hipersys-team/lightning/rtl/sram/nonlinear_lut/log_lut.v

       log_lut[1] = 3; // log(32) = 3.4657359027997265
       log_lut[2] = 4; // log(64) = 4.1588830833596715
       log_lut[3] = 4; // log(96) = 4.564348191467836
       log_lut[4] = 4; // log(128) = 4.852030263919617
       log_lut[5] = 5; // log(160) = 5.075173815233827
       log_lut[6] = 5; // log(192) = 5.2574953720277815
       log_lut[7] = 5; // log(224) = 5.4116460518550396
       log_lut[8] = 5; // log(256) = 5.545177444479562
       log_lut[9] = 5; // log(288) = 5.662960480135946
       log_lut[10] = 5; // log(320) = 5.768320995793772
       log_lut[11] = 5; // log(352) = 5.863631175598097
       log_lut[12] = 5; // log(384) = 5.950642552587727
       log_lut[13] = 6; // log(416) = 6.030685260261263
       log_lut[14] = 6; // log(448) = 6.104793232414985
       log_lut[15] = 6; // log(480) = 6.173786103901937
       log_lut[16] = 6; // log(512) = 6.238324625039508
       log_lut[17] = 6; // log(544) = 6.298949246855942
       log_lut[18] = 6; // log(576) = 6.3561076606958915
       log_lut[19] = 6; // log(608) = 6.410174881966167
       log_lut[20] = 6; // log(640) = 6.461468176353717
       log_lut[21] = 6; // log(672) = 6.51025834052315
       log_lut[22] = 6; // log(704) = 6.556778356158042
       log_lut[23] = 6; // log(736) = 6.601230118728877
       log_lut[24] = 6; // log(768) = 6.643789733147672
       log_lut[25] = 6; // log(800) = 6.684611727667927
       log_lut[26] = 6; // log(832) = 6.723832440821209
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
       log_lut[1983] = 11; // log(63456) = 11.058102031319523
       log_lut[1984] = 11; // log(63488) = 11.058606190644545
       log_lut[1985] = 11; // log(63520) = 11.059110095921017
       log_lut[1986] = 11; // log(63552) = 11.059613747404844
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
